steve-caiula/Temperature-LCD/hardware/hardware.kicad_sch

## KiCad design hardware/hardware.kicad_sch (2026-03-03)

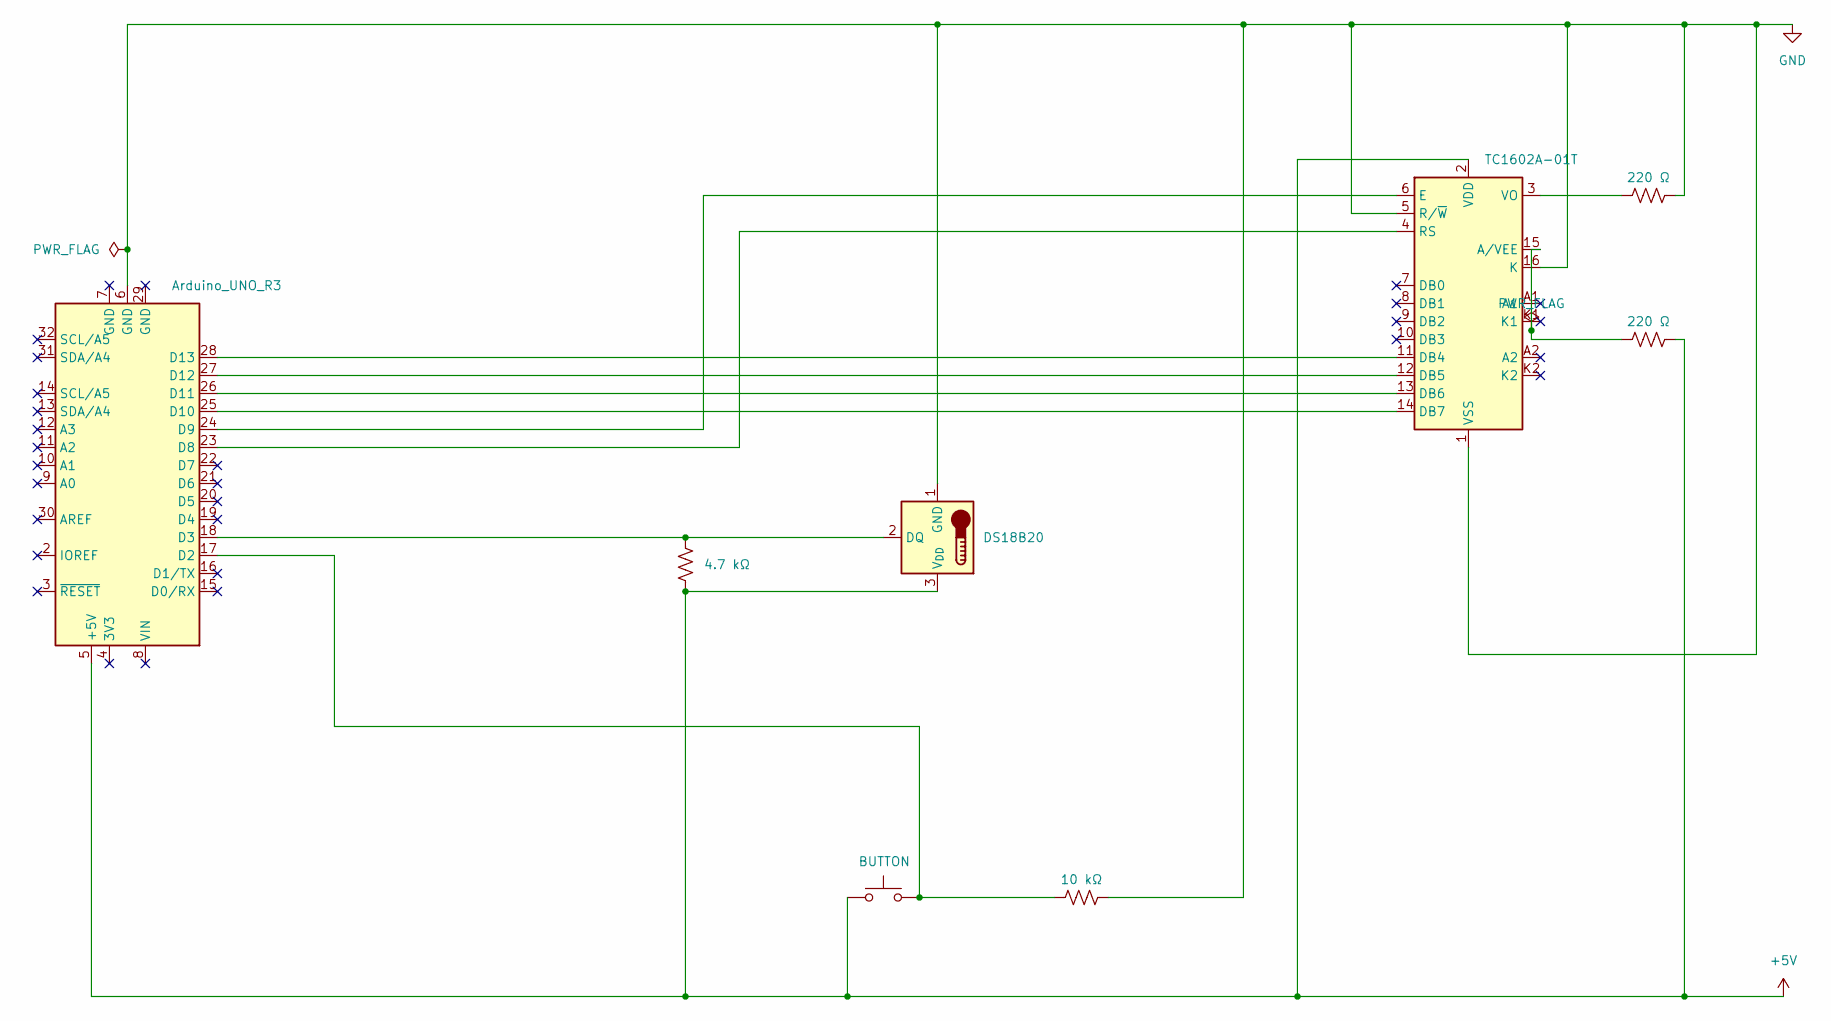
[picture p7: schematic hardware.kicad_sch]

Parts:
A1: Arduino_UNO_R3
R1: 10 kΩ
R2: 4.7 kΩ
R3, R4: 220 Ω
SW1: BUTTON
U1: TC1602A-01T
U2: DS18B20; TO-92_Inline

Connections:
+5V: A1.5 (+5V), R2.2, R4.2, SW1.1, U1.2 (VDD), U2.3 (V_{DD})
GND: A1.6 (GND), R1.2, R3.2, U1.1 (VSS), U1.5 (R/~W), U1.16 (K), U2.1 (GND)
unnamed: A1.17 (D2), R1.1, SW1.2
unnamed: A1.18 (D3), R2.1, U2.2 (DQ)
unnamed: A1.23 (D8), U1.4 (RS)
unnamed: A1.24 (D9), U1.6 (E)
unnamed: A1.25 (D10), U1.14 (DB7)
unnamed: A1.26 (D11), U1.13 (DB6)
unnamed: A1.27 (D12), U1.12 (DB5)
unnamed: A1.28 (D13), U1.11 (DB4)
unnamed: R3.1, U1.3 (VO)
unnamed: R4.1, U1.15 (A/VEE)
