steve-caiula/Temperature-LCD/include/pin_definitions.h

// --- PIN DEFINITIONS ---

#ifndef PIN_DEF
#define PIN_DEF

// BUTTON PIN
#define BUTTON PD2

// SENSOR PIN
#define TEMP_SENSOR PD3

// LCD PINS
#define LCD_RS  PB0
#define LCD_E   PB1
#define LCD_DB4 PB2
#define LCD_DB5 PB3
#define LCD_DB6 PB4
#define LCD_DB7 PB5

#endif
